jonsag/pi-heating/Documents/images/ardPowerTempLog-pcb_bottom.JPG

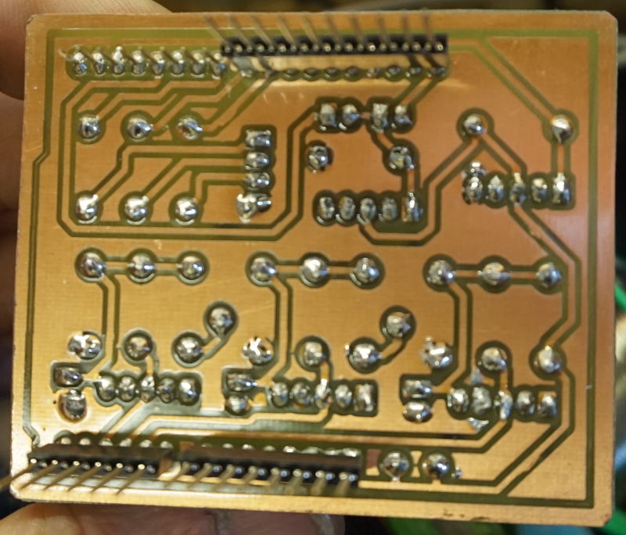
Documents/images/ardPowerTempLog-pcb_bottom.JPG
