jonsag/pi-heating/Arduino sketches/nmDiscover1WireDevices-pio/src/config.h

String programName = "nmDiscover1WireDevices";
String date = "20211129";
String author = "Jon Sagebrand";
String email = "jonsagebrand@gmail.com";

/***********
   DHT config
 ***********/
const int dsPin = 0; // Connect DHT sensor to GPIO0, D3

/***********
   Misc
 ***********/
int deviceCount;
