jonsag/pi-heating/Arduino sketches/nmDHTweb-pio/src/wifi.h

#include <ESP8266WiFi.h>

void setup_wifi()
{
  delay(100);

  Serial.println("");
  Serial.print("Connecting to ");
  Serial.println(ssid);
  WiFi.begin(ssid, password);
  while (WiFi.status() != WL_CONNECTED)
  {
    delay(500);
    Serial.print(".");
  }

  randomSeed(micros());

  Serial.println("");
  Serial.println("WiFi connected");
  Serial.print("IP address: ");
  Serial.println(WiFi.localIP());
  Serial.print("Web server port: ");
  Serial.println(serverPort);
  Serial.println();
}
